ChrisChrisLoLo/beyblock20/images/PXL_20220821_183053849.jpg

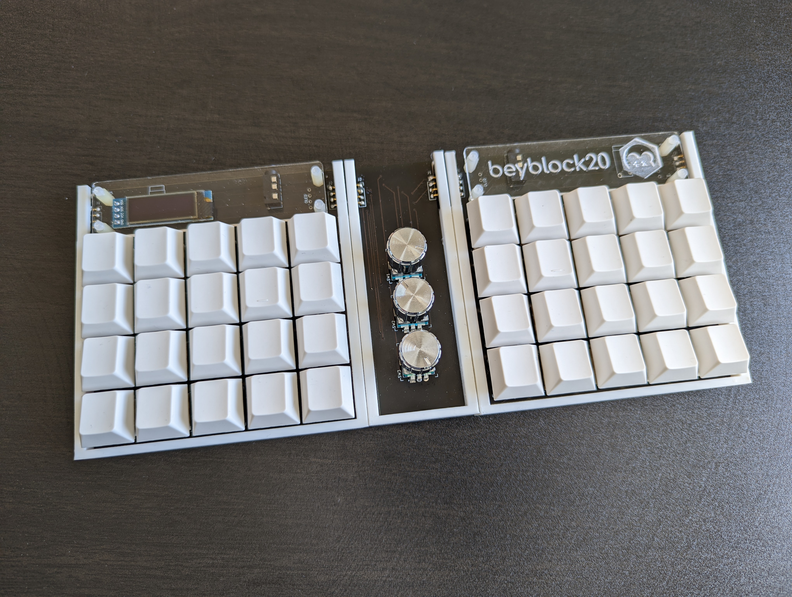
images/PXL_20220821_183053849.jpg
