ChrisChrisLoLo/beyblock20/images/PXL_20220821_183204263.jpg

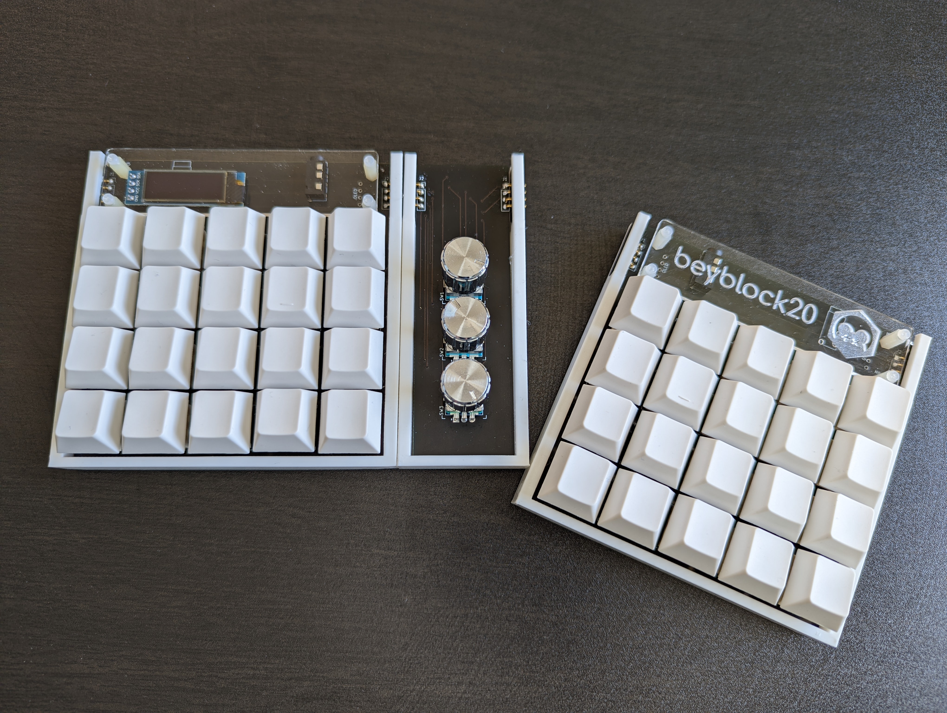
images/PXL_20220821_183204263.jpg
