ChrisChrisLoLo/beyblock20/images/PXL_20220821_184055940.jpg

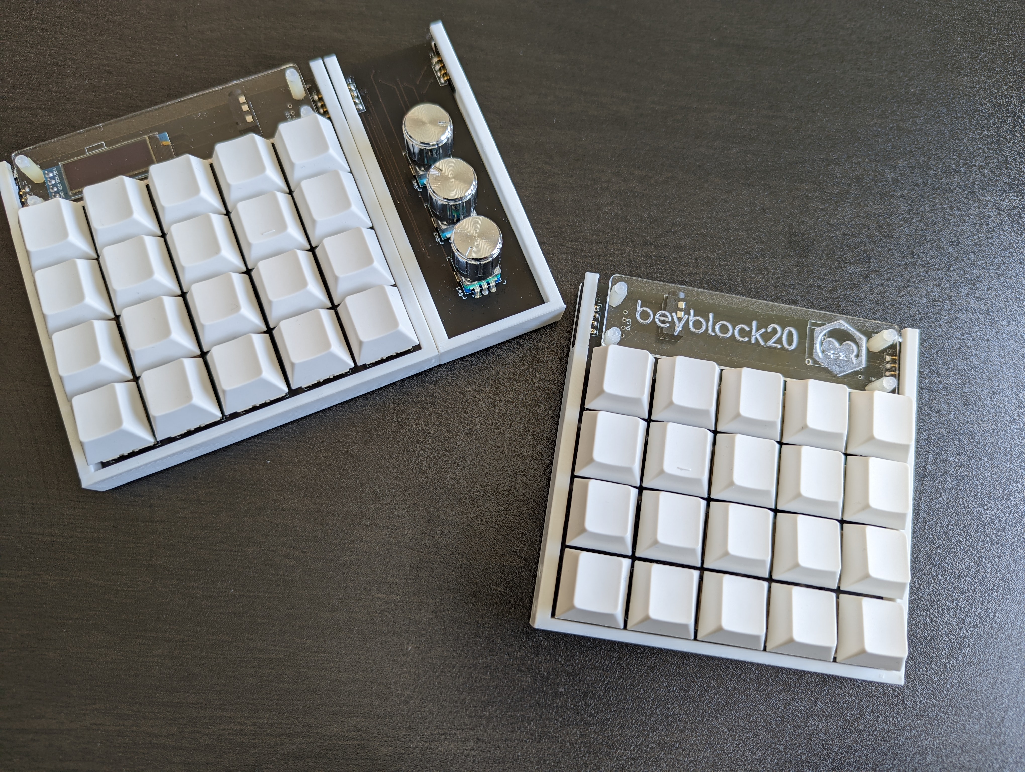
images/PXL_20220821_184055940.jpg
