ChrisChrisLoLo/beyblock20/images/PXL_20220821_184402483.jpg

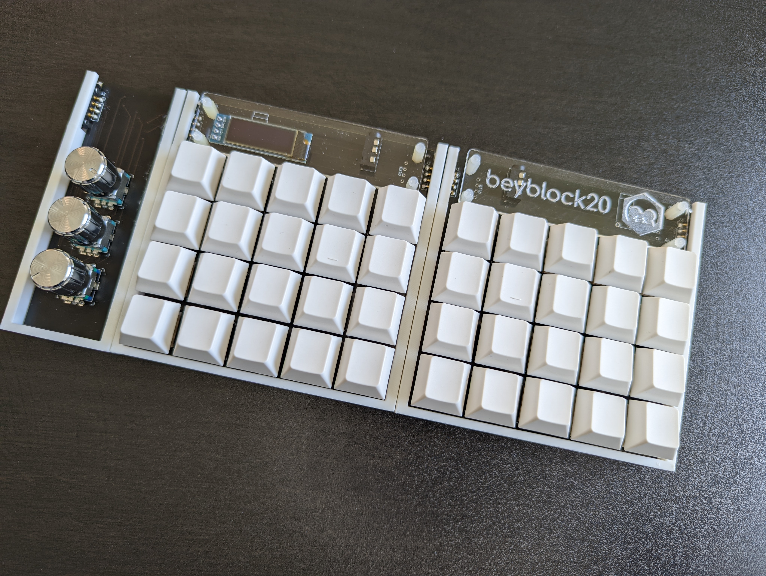
images/PXL_20220821_184402483.jpg
