ChrisChrisLoLo/beyblock20/pcb/knoblin3/knoblin3.kicad_sch

## KiCad design pcb/knoblin3/knoblin3.kicad_sch (2022-09-18, an earlier design)

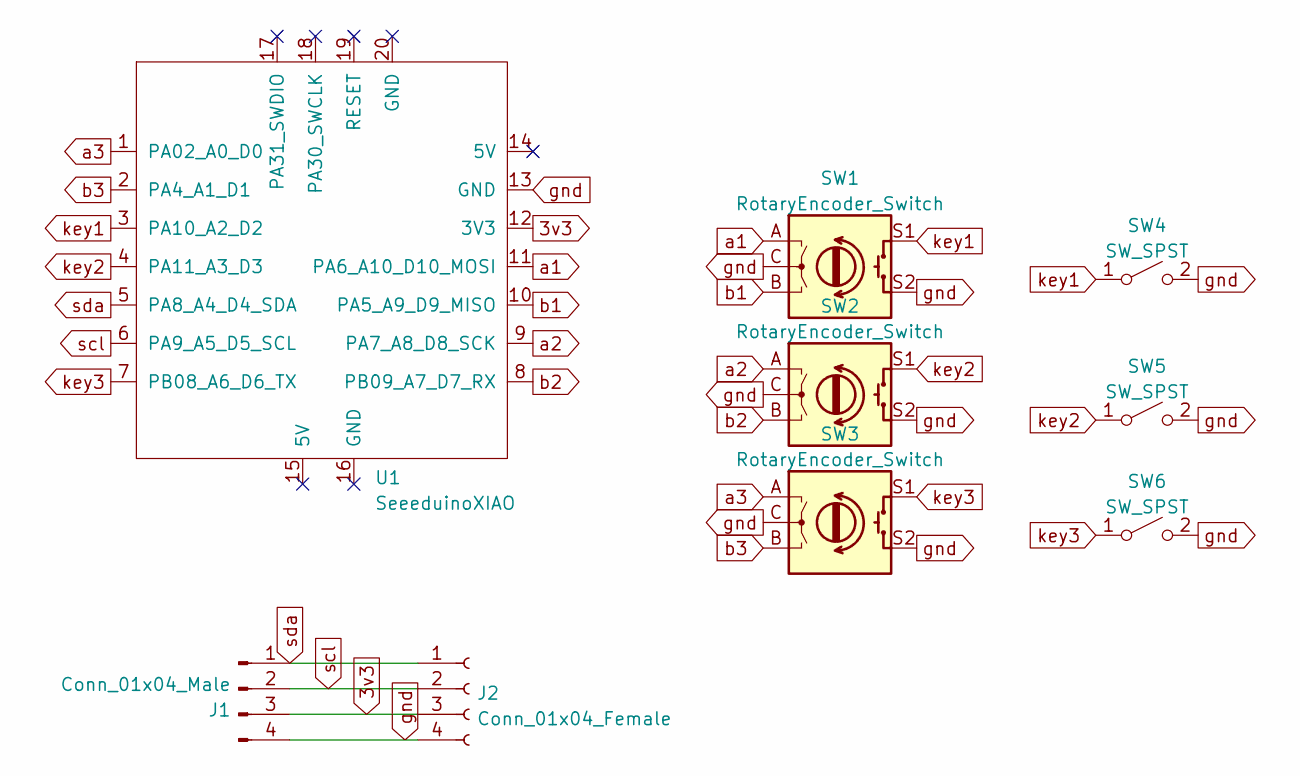
[picture p22: schematic knoblin3.kicad_sch]

Parts:
J1: Conn_01x04_Male; PinSocket_1x04_P2.54mm_Vertical
J2: Conn_01x04_Female; PinSocket_1x04_P2.54mm_Vertical
SW1, SW2, SW3: RotaryEncoder_Switch; RotaryEncoder_Alps_EC11E-Switch_Vertical_H20mm
SW4, SW5, SW6: SW_SPST; Kailh_socket_MX
U1: SeeeduinoXIAO; Seeeduino XIAO-MOUDLE14P-2.54-21X17.8MM

Connections:
3v3: J1.3, J2.3, U1.12 (3V3)
a1: SW1.A, U1.11 (PA6_A10_D10_MOSI)
a2: SW2.A, U1.9 (PA7_A8_D8_SCK)
a3: SW3.A, U1.1 (PA02_A0_D0)
b1: SW1.B, U1.10 (PA5_A9_D9_MISO)
b2: SW2.B, U1.8 (PB09_A7_D7_RX)
b3: SW3.B, U1.2 (PA4_A1_D1)
gnd: J1.4, J2.4, SW1.C, SW1.S2, SW2.C, SW2.S2, SW3.C, SW3.S2, SW4.2 (B), SW5.2 (B), SW6.2 (B), U1.13 (GND)
key1: SW1.S1, SW4.1 (A), U1.3 (PA10_A2_D2)
key2: SW2.S1, SW5.1 (A), U1.4 (PA11_A3_D3)
key3: SW3.S1, SW6.1 (A), U1.7 (PB08_A6_D6_TX)
scl: J1.2, J2.2, U1.6 (PA9_A5_D5_SCL)
sda: J1.1, J2.1, U1.5 (PA8_A4_D4_SDA)
