ChrisChrisLoLo/beyblock20/pcb/mongus48/mongus48.kicad_sch

## KiCad design pcb/mongus48/mongus48.kicad_sch (2022-09-29, an earlier design)

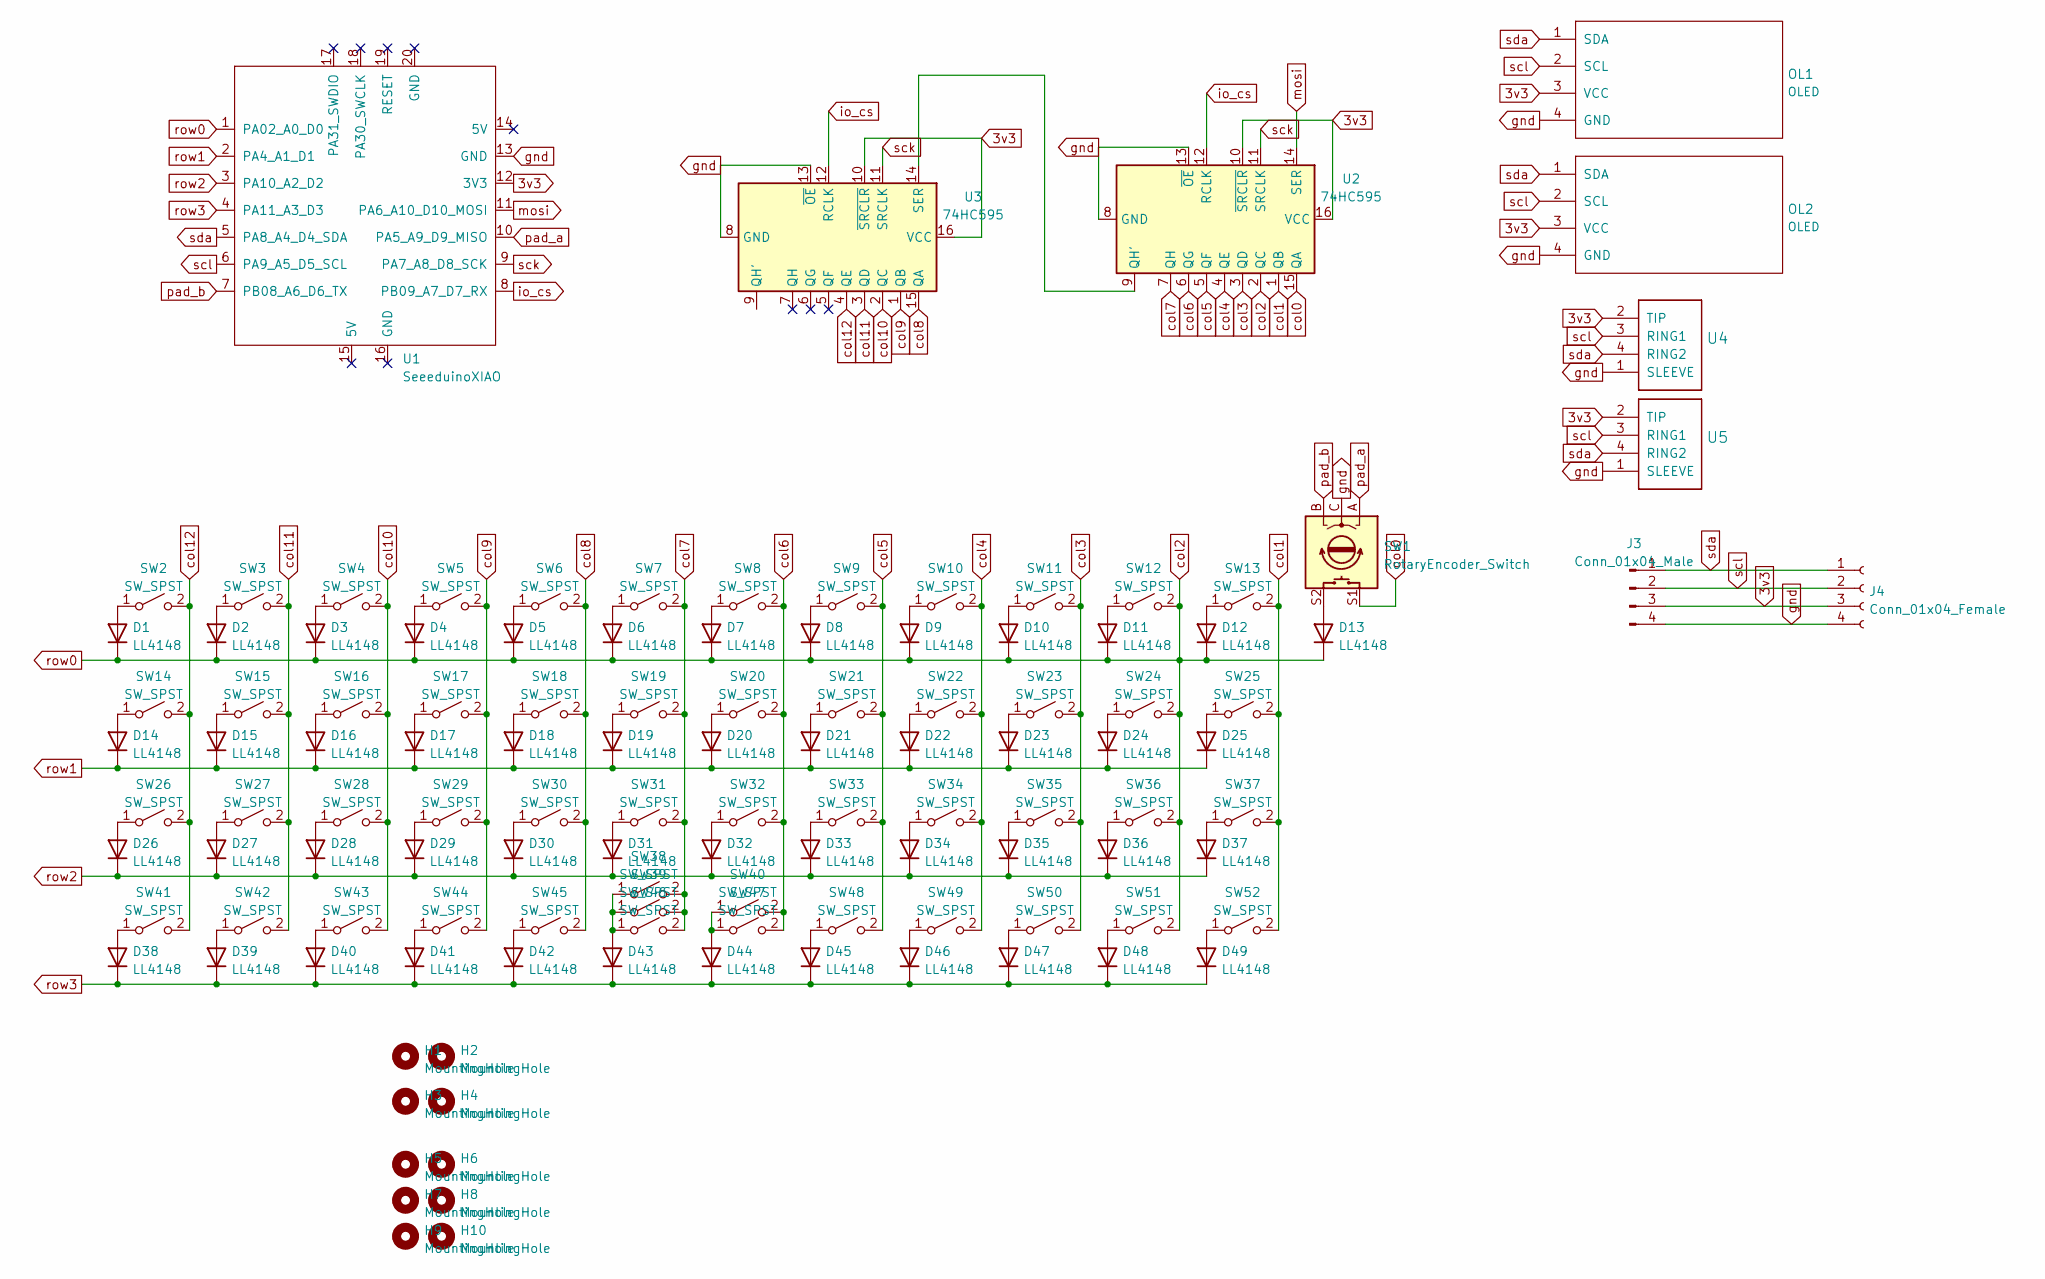
[picture p23: schematic mongus48.kicad_sch]

Parts:
D1, D2, D3, D4, D5, D6, D7, D8, D9, D10, D11, D12, D13, D14, D15, D16, D17, D18, D19, D20, D21, D22, D23, D24, D25, D26, D27, D28, D29, D30, D31, D32, D33, D34, D35, D36, D37, D38, D39, D40, D41, D42, D43, D44, D45, D46, D47, D48, D49: LL4148; D_MiniMELF
H1, H2, H3, H4, H5, H6, H7, H8, H9, H10: MountingHole
J3: Conn_01x04_Male
J4: Conn_01x04_Female
OL1, OL2: OLED
SW1: RotaryEncoder_Switch
SW2, SW3, SW4, SW5, SW6, SW7, SW8, SW9, SW10, SW11, SW12, SW13, SW14, SW15, SW16, SW17, SW18, SW19, SW20, SW21, SW22, SW23, SW24, SW25, SW26, SW27, SW28, SW29, SW30, SW31, SW32, SW33, SW34, SW35, SW36, SW37, SW38, SW39, SW40, SW41, SW42, SW43, SW44, SW45, SW46, SW47, SW48, SW49, SW50, SW51, SW52: SW_SPST
U1: SeeeduinoXIAO
U2, U3: 74HC595
U4, U5: (no value)

Connections:
3v3: J3.3, J4.3, OL1.3 (VCC), OL2.3 (VCC), U1.12 (3V3), U2.10 (~SRCLR), U2.16 (VCC), U3.10 (~SRCLR), U3.16 (VCC), U4.2 (TIP), U5.2 (TIP)
unnamed: D1.2 (A), SW2.1 (A)
unnamed: D2.2 (A), SW3.1 (A)
unnamed: D3.2 (A), SW4.1 (A)
unnamed: D4.2 (A), SW5.1 (A)
unnamed: D5.2 (A), SW6.1 (A)
unnamed: D6.2 (A), SW7.1 (A)
unnamed: D7.2 (A), SW8.1 (A)
unnamed: D8.2 (A), SW9.1 (A)
unnamed: D9.2 (A), SW10.1 (A)
unnamed: D10.2 (A), SW11.1 (A)
unnamed: D11.2 (A), SW12.1 (A)
unnamed: D12.2 (A), SW13.1 (A)
unnamed: D13.2 (A), SW1.S2
unnamed: D14.2 (A), SW14.1 (A)
unnamed: D15.2 (A), SW15.1 (A)
unnamed: D16.2 (A), SW16.1 (A)
unnamed: D17.2 (A), SW17.1 (A)
unnamed: D18.2 (A), SW18.1 (A)
unnamed: D19.2 (A), SW19.1 (A)
unnamed: D20.2 (A), SW20.1 (A)
unnamed: D21.2 (A), SW21.1 (A)
unnamed: D22.2 (A), SW22.1 (A)
unnamed: D23.2 (A), SW23.1 (A)
unnamed: D24.2 (A), SW24.1 (A)
unnamed: D25.2 (A), SW25.1 (A)
unnamed: D26.2 (A), SW26.1 (A)
unnamed: D27.2 (A), SW27.1 (A)
unnamed: D28.2 (A), SW28.1 (A)
unnamed: D29.2 (A), SW29.1 (A)
unnamed: D30.2 (A), SW30.1 (A)
unnamed: D31.2 (A), SW31.1 (A)
unnamed: D32.2 (A), SW32.1 (A)
unnamed: D33.2 (A), SW33.1 (A)
unnamed: D34.2 (A), SW34.1 (A)
unnamed: D35.2 (A), SW35.1 (A)
unnamed: D36.2 (A), SW36.1 (A)
unnamed: D37.2 (A), SW37.1 (A)
unnamed: D38.2 (A), SW41.1 (A)
unnamed: D39.2 (A), SW42.1 (A)
unnamed: D40.2 (A), SW43.1 (A)
unnamed: D41.2 (A), SW44.1 (A)
unnamed: D42.2 (A), SW45.1 (A)
unnamed: D43.2 (A), SW38.1 (A), SW39.1 (A), SW46.1 (A)
unnamed: D44.2 (A), SW40.1 (A), SW47.1 (A)
unnamed: D45.2 (A), SW48.1 (A)
unnamed: D46.2 (A), SW49.1 (A)
unnamed: D47.2 (A), SW50.1 (A)
unnamed: D48.2 (A), SW51.1 (A)
unnamed: D49.2 (A), SW52.1 (A)
unnamed: U2.9 (QH'), U3.14 (SER)
col0: SW1.S1, U2.15 (QA)
col1: SW13.2 (B), SW25.2 (B), SW37.2 (B), SW52.2 (B), U2.1 (QB)
col2: D1.1 (K), D2.1 (K), D3.1 (K), D4.1 (K), D5.1 (K), D6.1 (K), D7.1 (K), D8.1 (K), D9.1 (K), D10.1 (K), D11.1 (K), D12.1 (K), D13.1 (K), SW12.2 (B), SW24.2 (B), SW36.2 (B), SW51.2 (B), U1.1 (PA02_A0_D0), U2.2 (QC)
col3: SW11.2 (B), SW23.2 (B), SW35.2 (B), SW50.2 (B), U2.3 (QD)
col4: SW10.2 (B), SW22.2 (B), SW34.2 (B), SW49.2 (B), U2.4 (QE)
col5: SW9.2 (B), SW21.2 (B), SW33.2 (B), SW48.2 (B), U2.5 (QF)
col6: SW8.2 (B), SW20.2 (B), SW32.2 (B), SW40.2 (B), SW47.2 (B), U2.6 (QG)
col7: SW7.2 (B), SW19.2 (B), SW31.2 (B), SW38.2 (B), SW39.2 (B), SW46.2 (B), U2.7 (QH)
col8: SW6.2 (B), SW18.2 (B), SW30.2 (B), SW45.2 (B), U3.15 (QA)
col9: SW5.2 (B), SW17.2 (B), SW29.2 (B), SW44.2 (B), U3.1 (QB)
col10: SW4.2 (B), SW16.2 (B), SW28.2 (B), SW43.2 (B), U3.2 (QC)
col11: SW3.2 (B), SW15.2 (B), SW27.2 (B), SW42.2 (B), U3.3 (QD)
col12: SW2.2 (B), SW14.2 (B), SW26.2 (B), SW41.2 (B), U3.4 (QE)
gnd: J3.4, J4.4, OL1.4 (GND), OL2.4 (GND), SW1.C, U1.13 (GND), U2.8 (GND), U2.13 (~OE), U3.8 (GND), U3.13 (~OE), U4.1 (SLEEVE), U5.1 (SLEEVE)
io_cs: U1.8 (PB09_A7_D7_RX), U2.12 (RCLK), U3.12 (RCLK)
mosi: U1.11 (PA6_A10_D10_MOSI), U2.14 (SER)
pad_a: SW1.A, U1.10 (PA5_A9_D9_MISO)
pad_b: SW1.B, U1.7 (PB08_A6_D6_TX)
row1: D14.1 (K), D15.1 (K), D16.1 (K), D17.1 (K), D18.1 (K), D19.1 (K), D20.1 (K), D21.1 (K), D22.1 (K), D23.1 (K), D24.1 (K), D25.1 (K), U1.2 (PA4_A1_D1)
row2: D26.1 (K), D27.1 (K), D28.1 (K), D29.1 (K), D30.1 (K), D31.1 (K), D32.1 (K), D33.1 (K), D34.1 (K), D35.1 (K), D36.1 (K), D37.1 (K), U1.3 (PA10_A2_D2)
row3: D38.1 (K), D39.1 (K), D40.1 (K), D41.1 (K), D42.1 (K), D43.1 (K), D44.1 (K), D45.1 (K), D46.1 (K), D47.1 (K), D48.1 (K), D49.1 (K), U1.4 (PA11_A3_D3)
sck: U1.9 (PA7_A8_D8_SCK), U2.11 (SRCLK), U3.11 (SRCLK)
scl: J3.2, J4.2, OL1.2 (SCL), OL2.2 (SCL), U1.6 (PA9_A5_D5_SCL), U4.3 (RING1), U5.3 (RING1)
sda: J3.1, J4.1, OL1.1 (SDA), OL2.1 (SDA), U1.5 (PA8_A4_D4_SDA), U4.4 (RING2), U5.4 (RING2)
